YOUSSNDR/PolySnake/programmes/Caméra/image recognition 2/Arrowdown.png

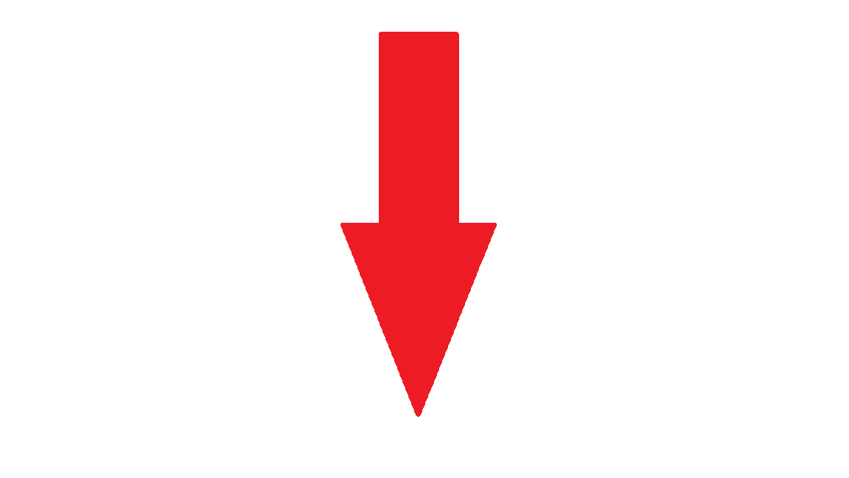
programmes/Caméra/image recognition 2/Arrowdown.png
