YOUSSNDR/PolySnake/programmes/Caméra/image recognition 5 (youss)/Arrown.png

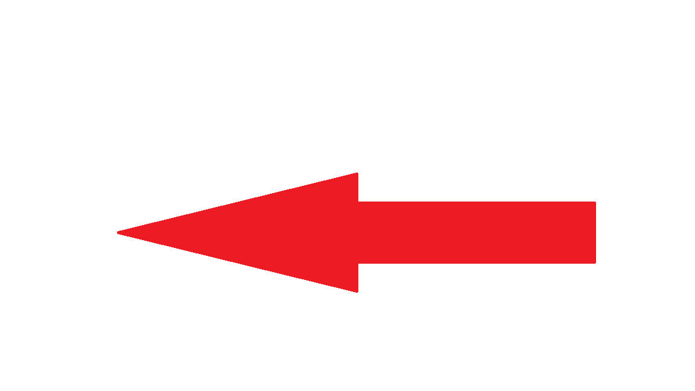
programmes/Caméra/image recognition 5 (youss)/Arrown.png
