YOUSSNDR/PolySnake/programmes/snake/snake2.0/raspberry2.0/Arrow.png

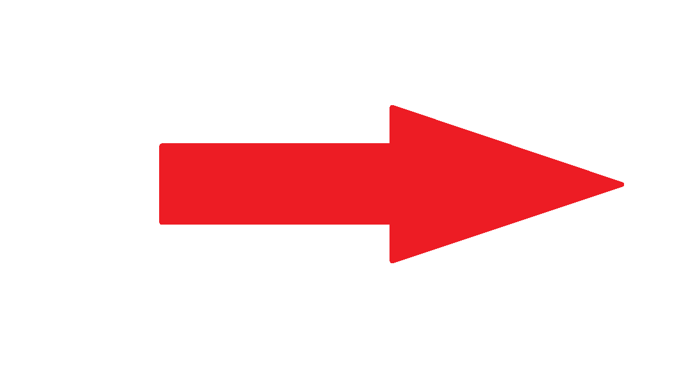
programmes/snake/snake2.0/raspberry2.0/Arrow.png
