YOUSSNDR/PolySnake/Rapports/Soufiani Younousse/images younousse/chargement raspberry1.jpg

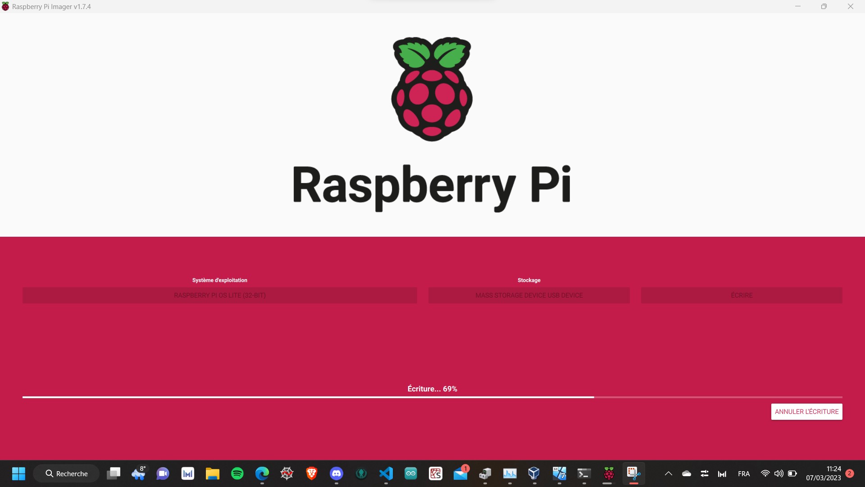
Rapports/Soufiani Younousse/images younousse/chargement raspberry1.jpg
