YOUSSNDR/PolySnake/Rapports/Soufiani Younousse/images younousse/chargement raspberry2.jpg

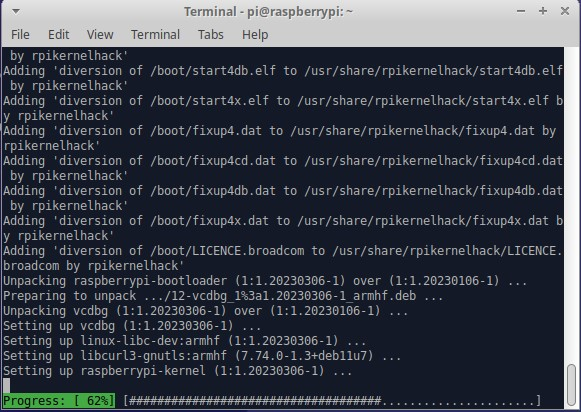
Rapports/Soufiani Younousse/images younousse/chargement raspberry2.jpg
