YOUSSNDR/PolySnake/Rapports/Soufiani Younousse/images younousse/IMG_20221209_102037_1.jpg

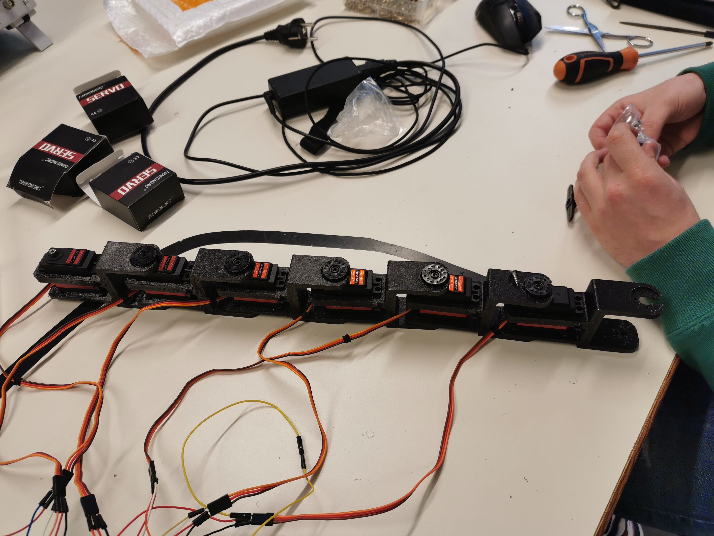
Rapports/Soufiani Younousse/images younousse/IMG_20221209_102037_1.jpg
