YOUSSNDR/PolySnake/Rapports/Soufiani Younousse/images younousse/IMG_20221209_102043.jpg

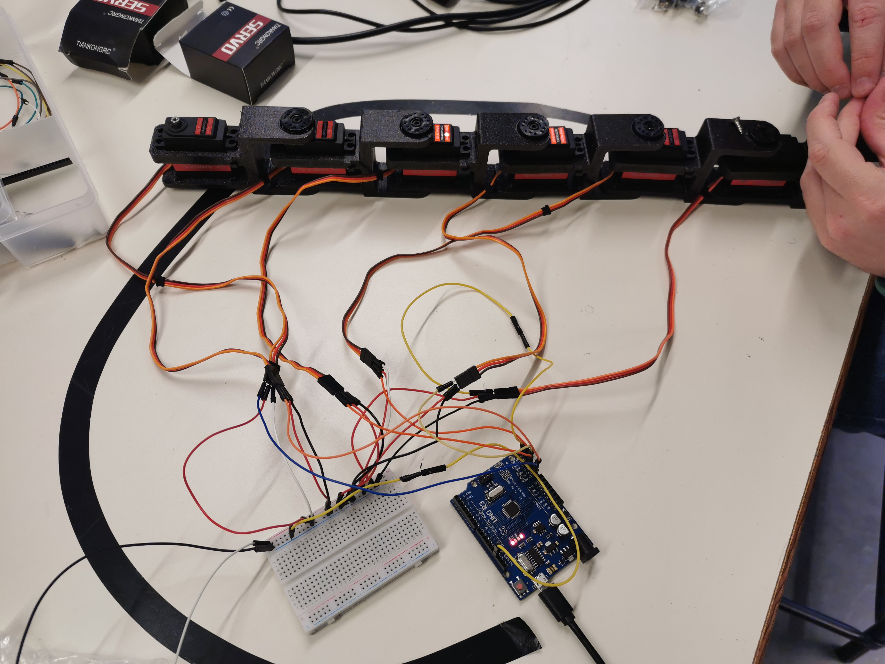
Rapports/Soufiani Younousse/images younousse/IMG_20221209_102043.jpg
