YOUSSNDR/PolySnake/Rapports/Soufiani Younousse/images younousse/IMG_20221209_102741.jpg

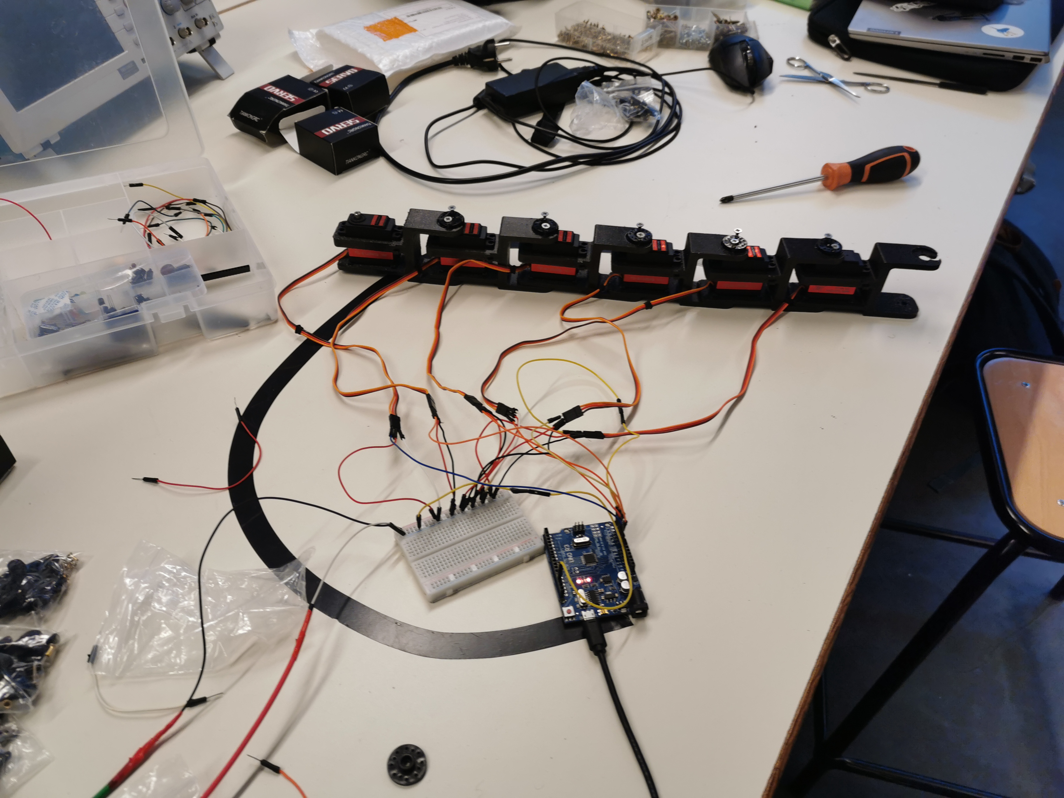
Rapports/Soufiani Younousse/images younousse/IMG_20221209_102741.jpg
