YOUSSNDR/PolySnake/Rapports/Soufiani Younousse/images younousse/IMG_20230106_102258.jpg

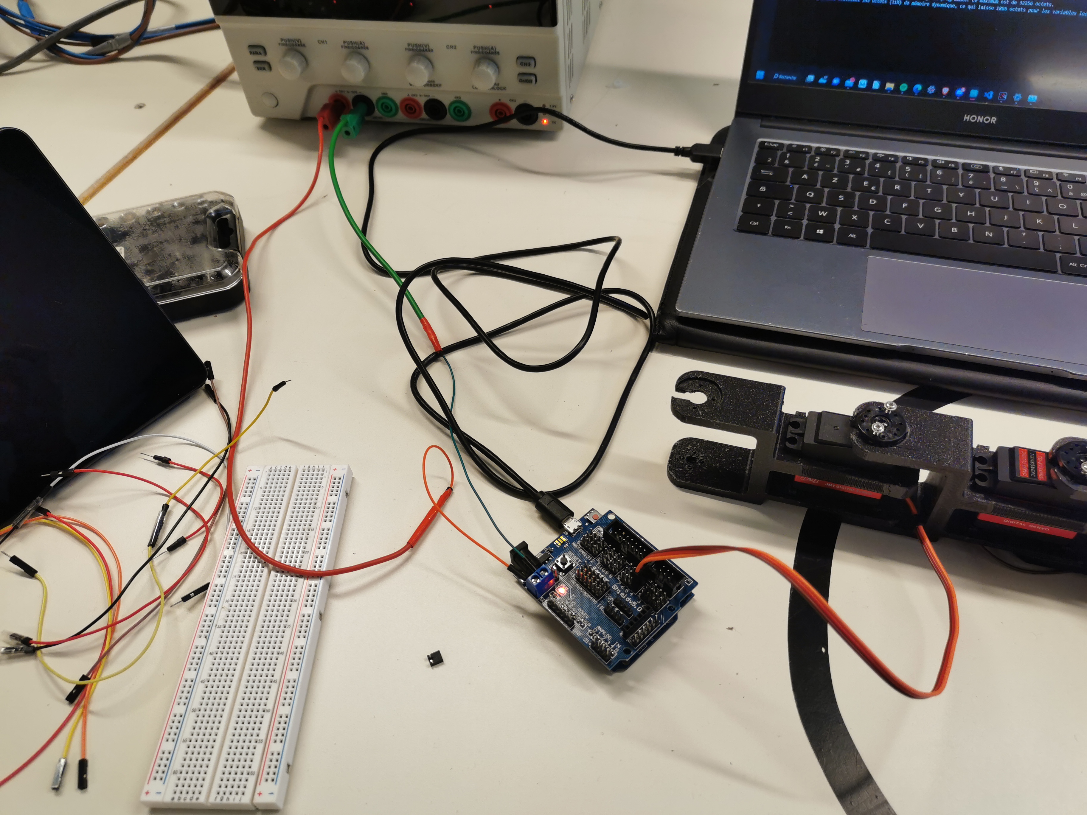
Rapports/Soufiani Younousse/images younousse/IMG_20230106_102258.jpg
