YOUSSNDR/PolySnake/Rapports/Soufiani Younousse/images younousse/IMG_20230106_104402.jpg

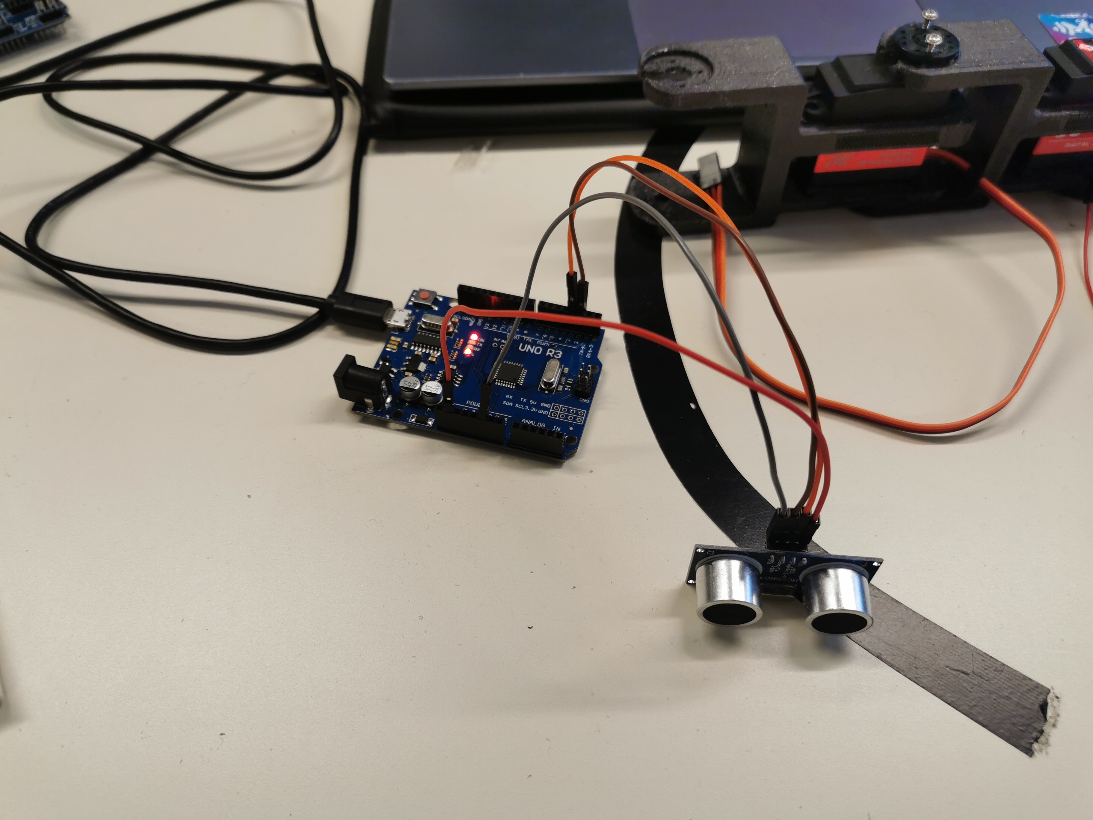
Rapports/Soufiani Younousse/images younousse/IMG_20230106_104402.jpg
