YOUSSNDR/PolySnake/Rapports/Soufiani Younousse/images younousse/IMG_20230113_120657.jpg

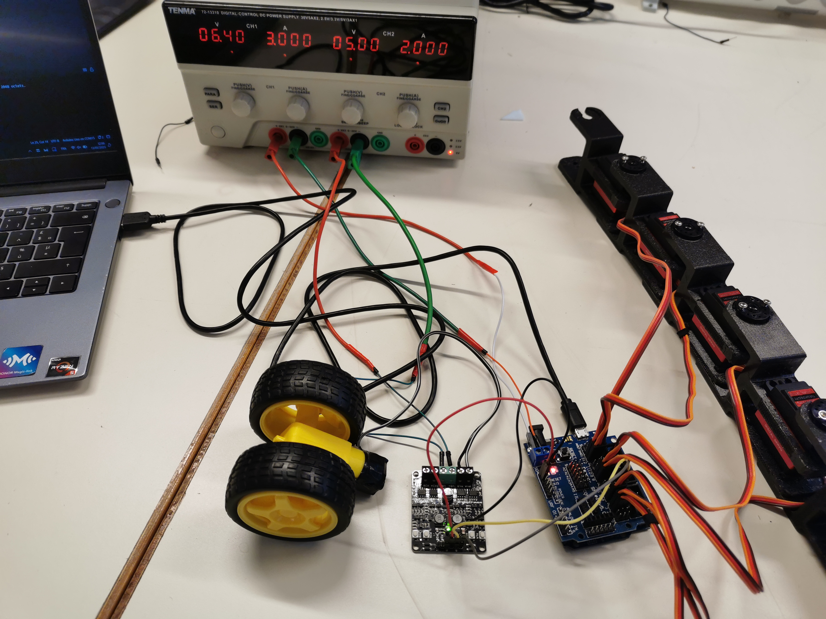
Rapports/Soufiani Younousse/images younousse/IMG_20230113_120657.jpg
