YOUSSNDR/PolySnake/Rapports/Soufiani Younousse/images younousse/IMG_20230114_164436.jpg

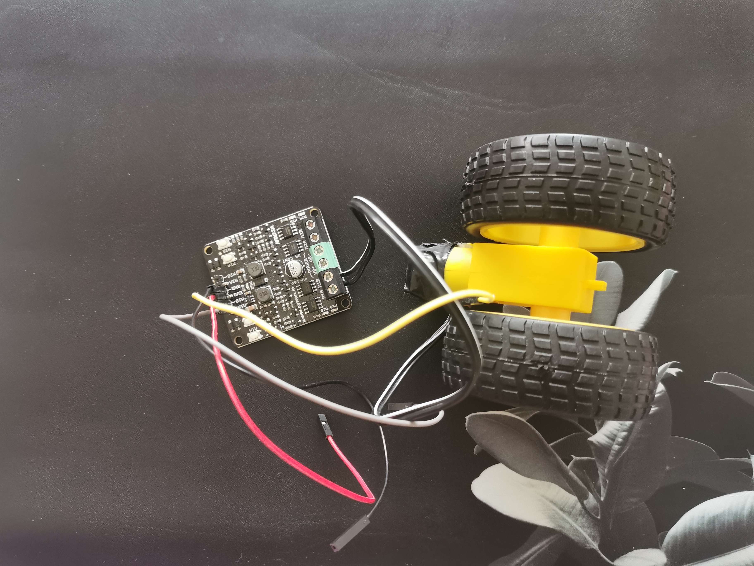
Rapports/Soufiani Younousse/images younousse/IMG_20230114_164436.jpg
