YOUSSNDR/PolySnake/Rapports/Soufiani Younousse/images younousse/info_slither.jpg

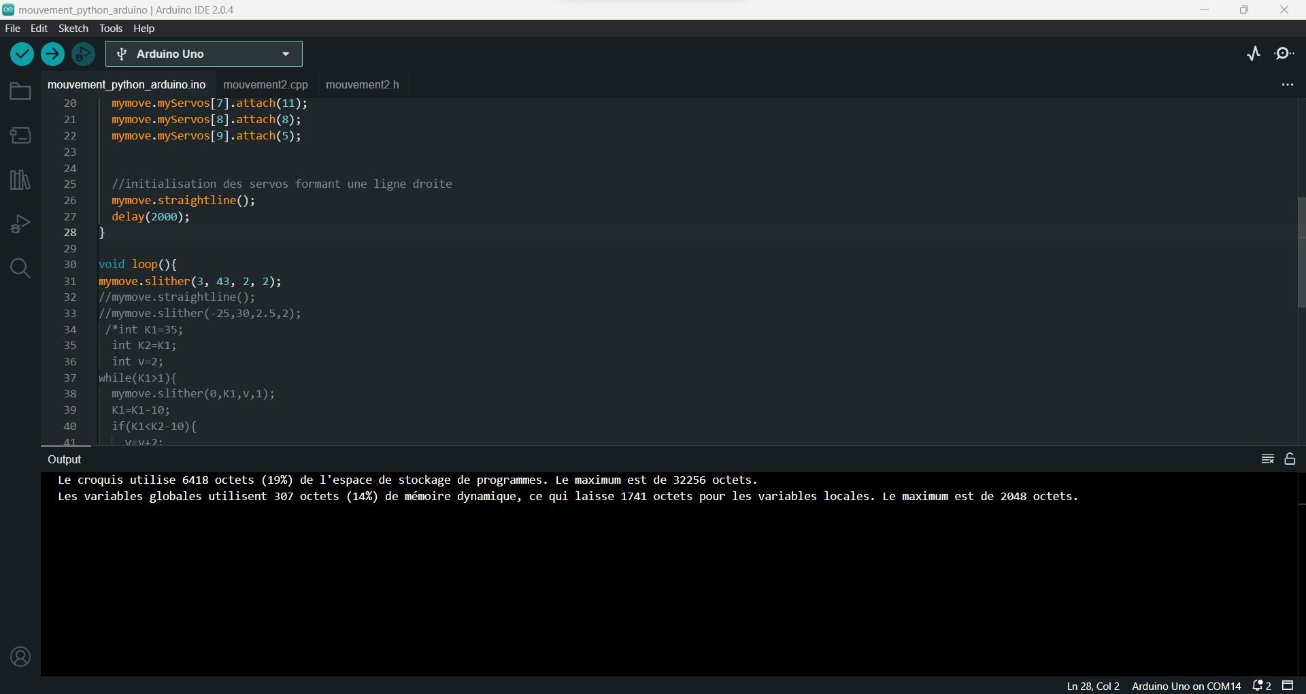
Rapports/Soufiani Younousse/images younousse/info_slither.jpg
