YOUSSNDR/PolySnake/Rapports/Soufiani Younousse/images younousse/mesure ultrason1.jpg

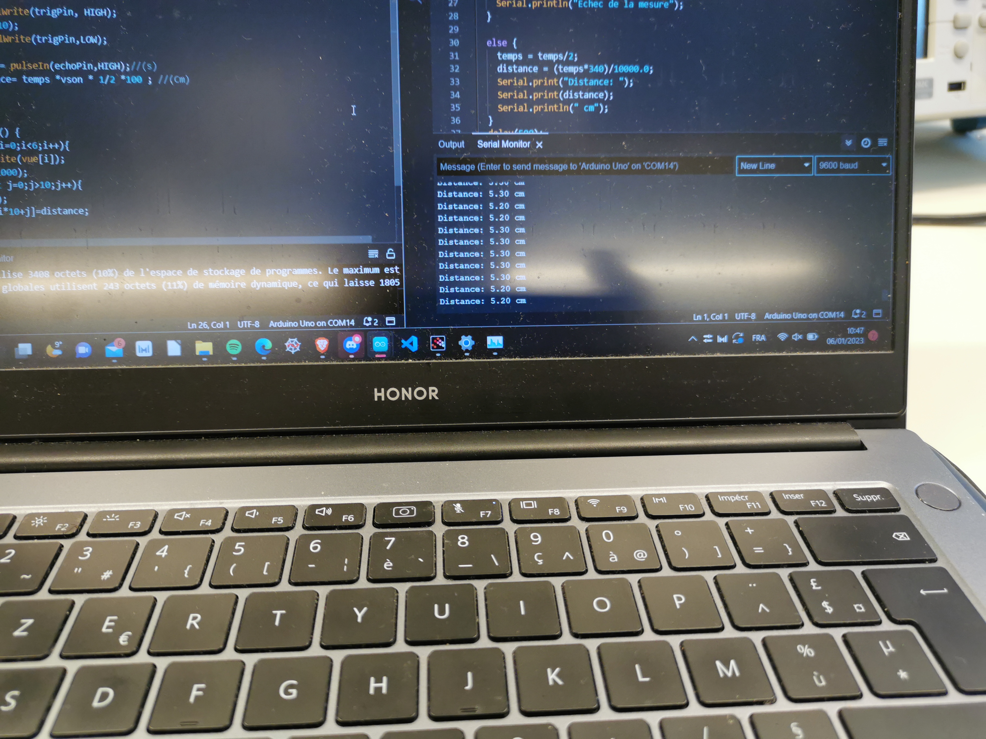
Rapports/Soufiani Younousse/images younousse/mesure ultrason1.jpg
