YOUSSNDR/PolySnake/Rapports/Soufiani Younousse/images younousse/myprogram1.jpg

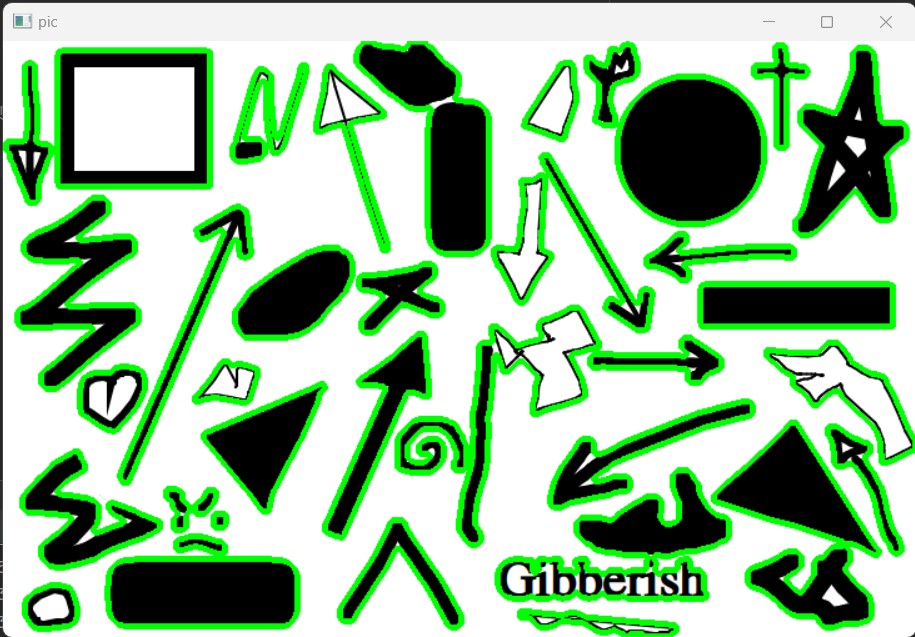
Rapports/Soufiani Younousse/images younousse/myprogram1.jpg
