YOUSSNDR/PolySnake/Rapports/Soufiani Younousse/images younousse/myprogram2.jpg

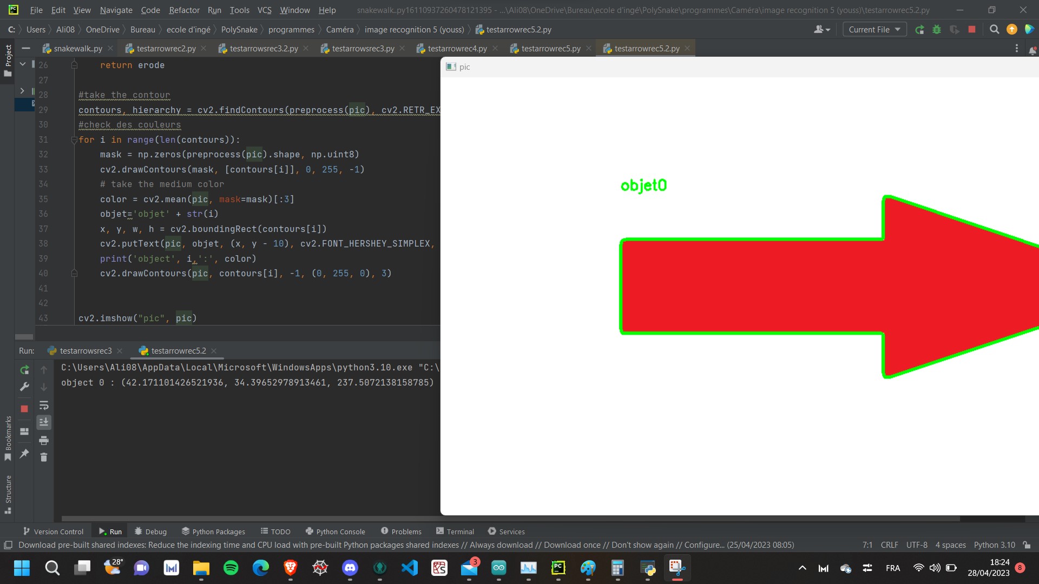
Rapports/Soufiani Younousse/images younousse/myprogram2.jpg
