YOUSSNDR/PolySnake/Rapports/Soufiani Younousse/images younousse/new connectics.jpg

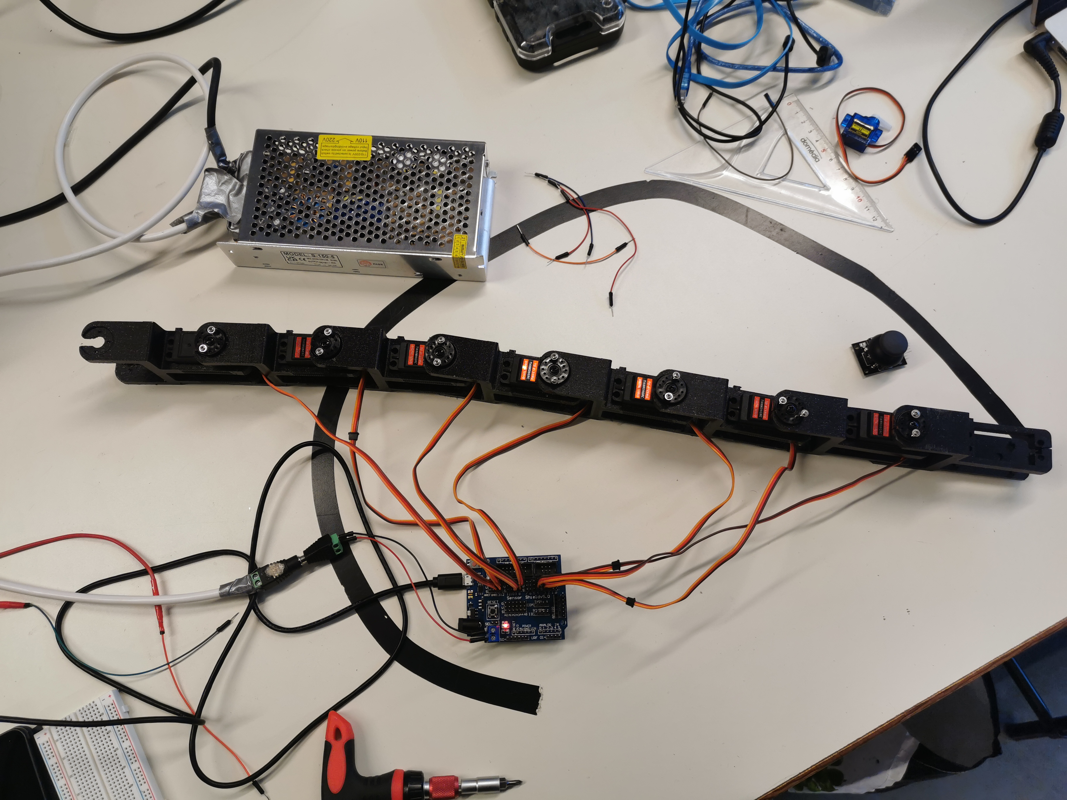
Rapports/Soufiani Younousse/images younousse/new connectics.jpg
