YOUSSNDR/PolySnake/Rapports/Soufiani Younousse/images younousse/serpent et roues.jpg

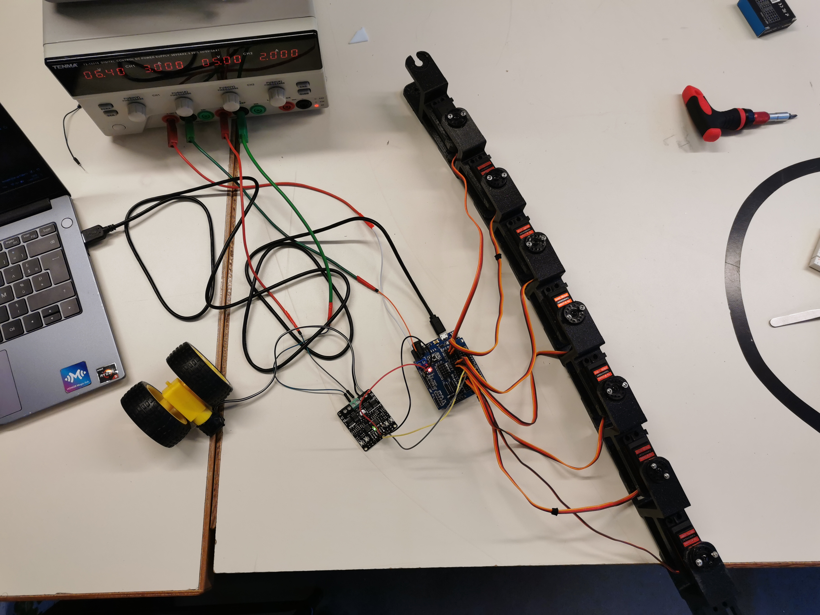
Rapports/Soufiani Younousse/images younousse/serpent et roues.jpg
