YOUSSNDR/PolySnake/Rapports/Soufiani Younousse/images younousse/first_test.jpg

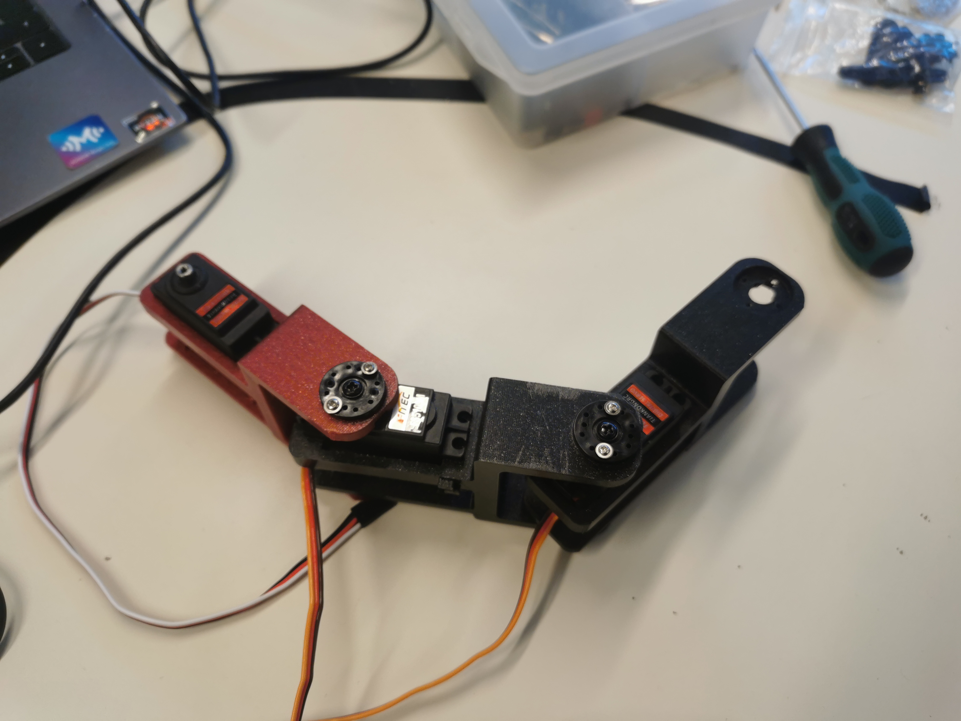
Rapports/Soufiani Younousse/images younousse/first_test.jpg
