YOUSSNDR/PolySnake/programmes/snake/snake2.0/arduino uno 2.0/mouvement2.0/mouvement2.0.ino

#include"mouvement2.0.h"
#include <Servo.h>

mouvement mymove;

void setup() {
  //we attach the different servos to their pin
  Serial.begin(9600); 
  mymove.myServos[0].attach(6);
  mymove.myServos[1].attach(7);
  mymove.myServos[2].attach(8);
  mymove.myServos[3].attach(9);
  mymove.myServos[4].attach(10);
  mymove.myServos[5].attach(11);
  mymove.myServos[6].attach(12);
  mymove.myServos[7].attach(13);
  //mymove.myServos[8].attach(8);
  //mymove.myServos[9].attach(5);

  
  //initialise the servos as a straightline
  mymove.straightline();
  delay(2000);
}

void loop(){
  x=Serial.readString().toInt(); //take the value comming from the raspberry
  condition, O, A, v, L= mymove.choose(x); // give the different value needed depending on "x"
  mymove.slither(O, A, v, L); //make the snke move with the given values

//for the test
//x=0
//mymove.slither(0, 43, 2, 1);
//mymove.straightline();

 /*int K1=35;
  int K2=K1;
  int v=2;
while(K1>1){
  mymove.slither(0,K1,v,1);
  K1=K1-10;
  if(K1<K2-10){
    v=v+2;
    K2=K2-10;
  }
  Serial.print(K1);
  Serial.print("   ");
  Serial.println(v);
  }
  for(int m=0;m>21;m++){
    mymove.slither(m,K1,v,1);
    delay(200);
  }
while(K1<35){
  mymove.slither(20,K1,v,1);
  K1=K1+10;
  if(K1>K2){
    v=v-2;
    K2=K2+10;
  }
  Serial.print(K1);
  Serial.print("   ");
  Serial.println(v);
}  
 for(int m=20;m<0;m--){
    mymove.slither(m,K1,v,1);
    delay(200);
 }*/
}
