YOUSSNDR/PolySnake/Algorythmie/mouvement2/mouvement2.ino

#include"mouvement.h"
#include <Servo.h>

mouvement mymove;

void setup() {//on initialise ici le moniteur série et attachons tous les servos selon le pin qui leur est attribué
  Serial.begin(9600);
  mymove.myServos[0].attach(2);
  mymove.myServos[1].attach(3);
  mymove.myServos[2].attach(4);
  mymove.myServos[3].attach(8);
  mymove.myServos[4].attach(9);
  mymove.myServos[5].attach(12);
  mymove.myServos[6].attach(13);
  mymove.myServos[7].attach(7);
  mymove.myServos[8].attach(8);
  mymove.myServos[9].attach(5);

  
  //initialisation des servos formant une ligne droite
  mymove.fLigne();
  delay(2000);
}

void loop(){
  //mymove.fOndulation(0, 30, 3, 1.5); //on active une ondulation sans décallage avec une aplitude de 30, une vitesse de 3, et une longueur d'onde de 1.5
  mymove.fLigne(); //on demande a tout les servos de se mettre en position initiale
}
