YOUSSNDR/PolySnake/programmes/communication/Test1_débugue/test.py

import serial
import time

arduino = serial.Serial(port='COM14', baudrate=115200, timeout=.1)


def write_read(x):
    arduino.write(bytes(x, 'utf-8'))
    time.sleep(0.05)
    data = arduino.readline()
    return data


while True:
    num = input("Enter a number: ")
    value = write_read(num)
    print(value)
